JaimeOrtegaxyz/artisans-memphis/output/color/01_ARCH_DOME.png

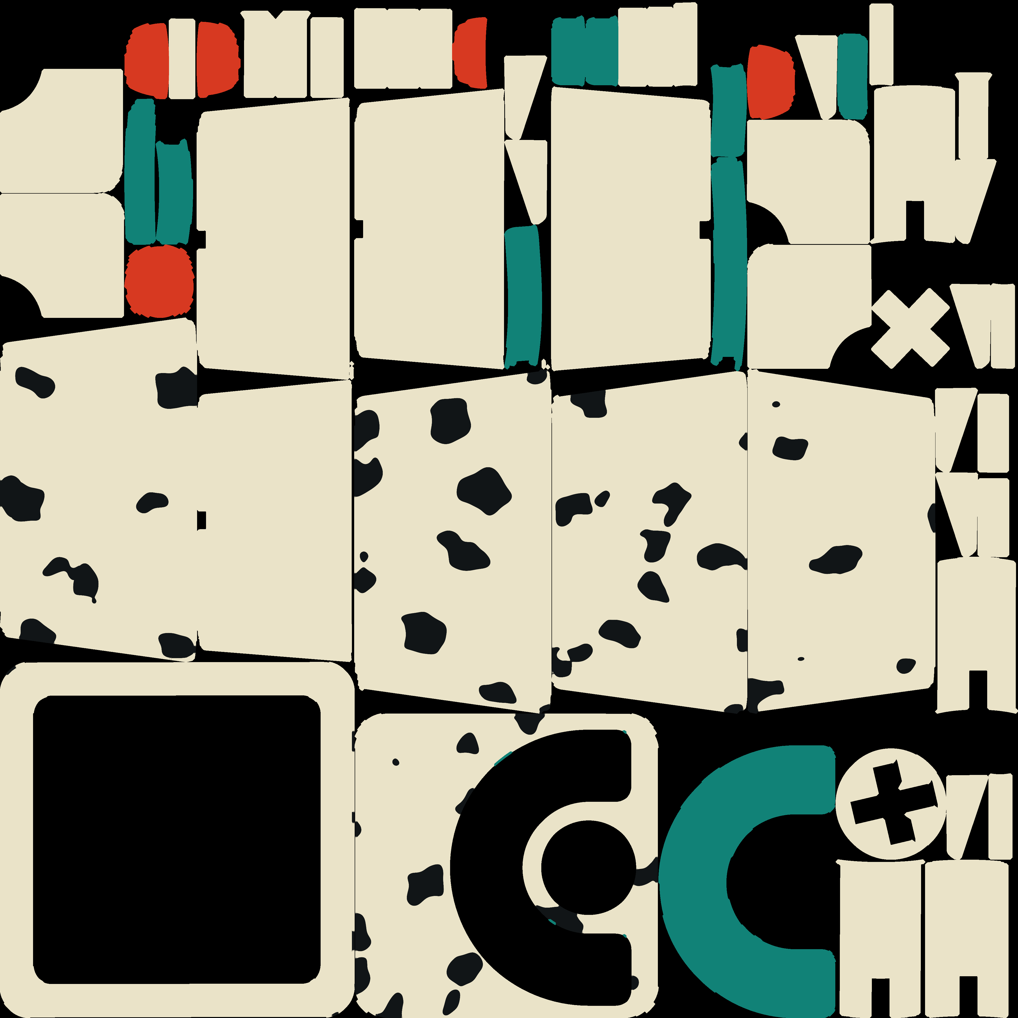
output/color/01_ARCH_DOME.png
