JaimeOrtegaxyz/artisans-memphis/output/color/02_ZIGZAG_CYLINDER.png

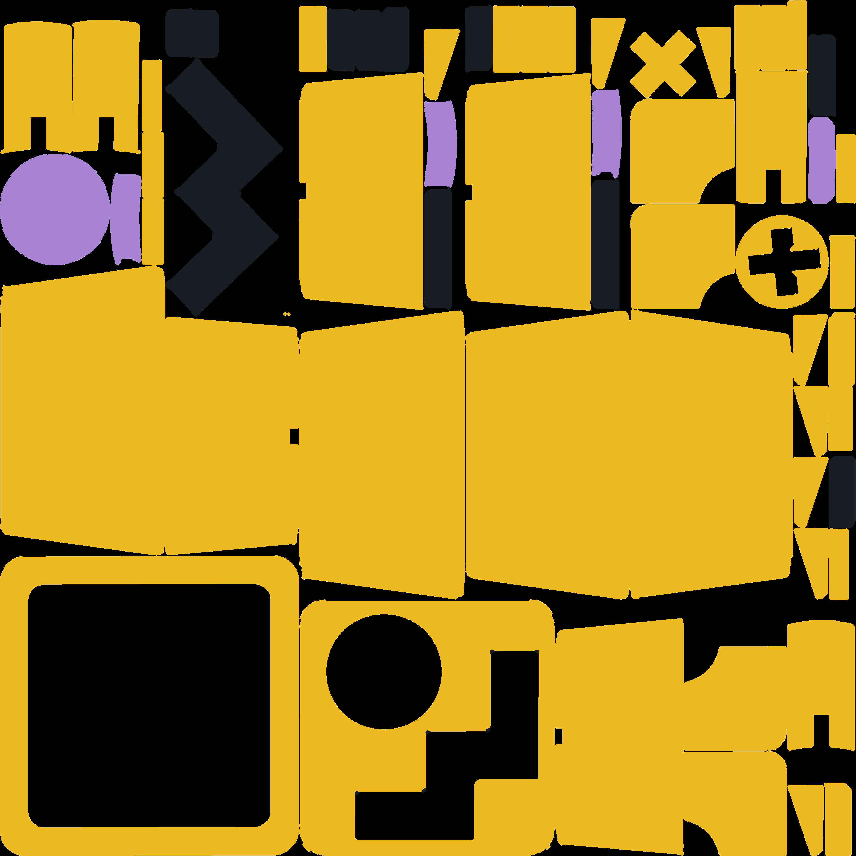
output/color/02_ZIGZAG_CYLINDER.png
