JaimeOrtegaxyz/artisans-memphis/output/color/03_DISC_RAILS.png

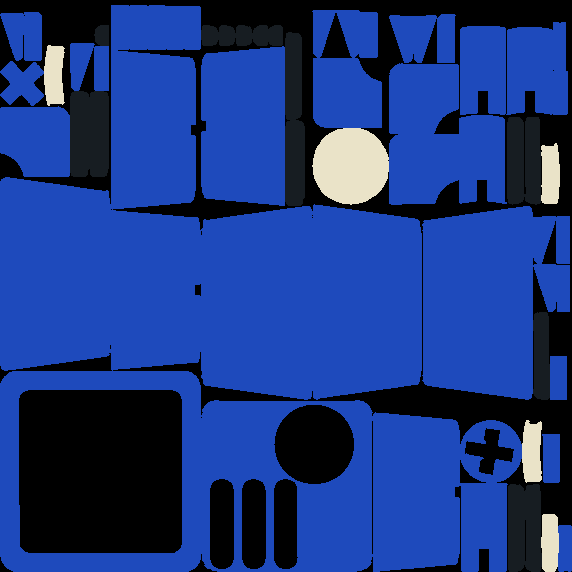
output/color/03_DISC_RAILS.png
