JaimeOrtegaxyz/artisans-memphis/output/color/04_STAIR_SILHOUETTE.png

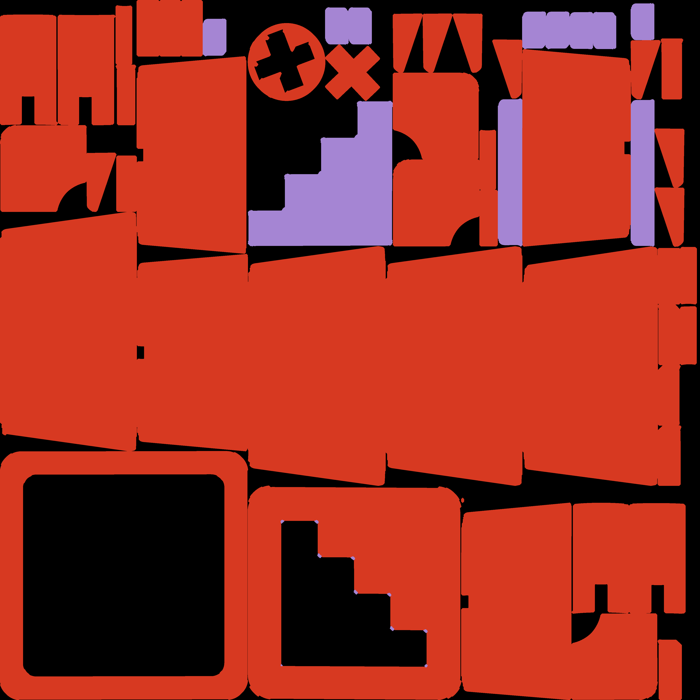
output/color/04_STAIR_SILHOUETTE.png
