JaimeOrtegaxyz/artisans-memphis/output/color/Color_Preview.png

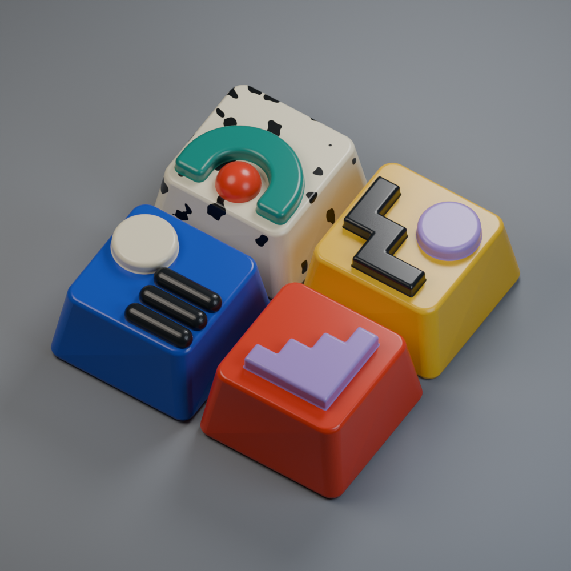
output/color/Color_Preview.png
