JaimeOrtegaxyz/artisans-memphis/output/drawings/04_STAIR_SILHOUETTE.png

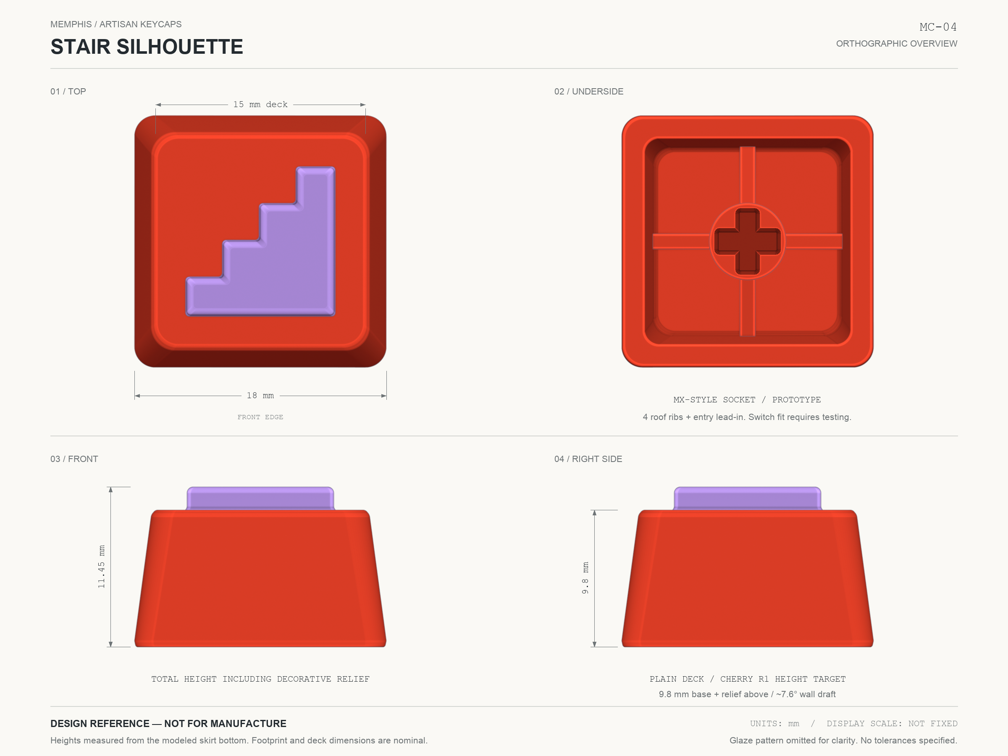
output/drawings/04_STAIR_SILHOUETTE.png
