JaimeOrtegaxyz/artisans-memphis/output/Memphis_Top.png

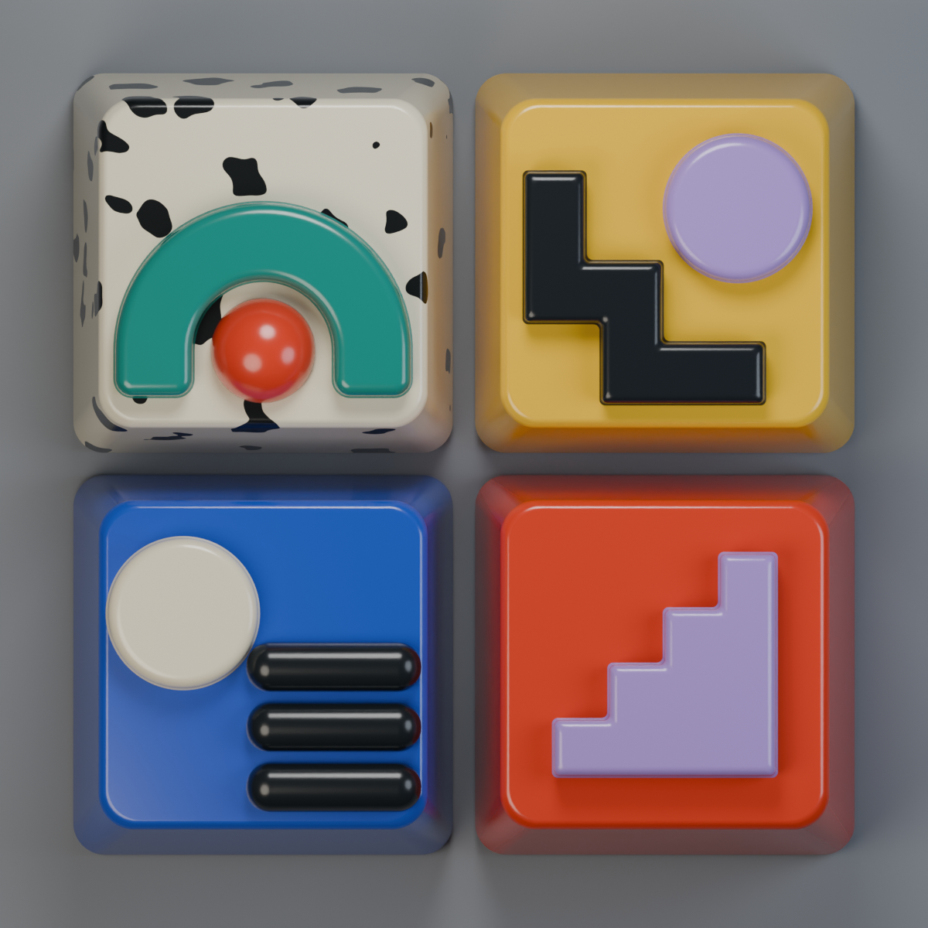
output/Memphis_Top.png
