JaimeOrtegaxyz/artisans-memphis/output/Memphis_Underside.png

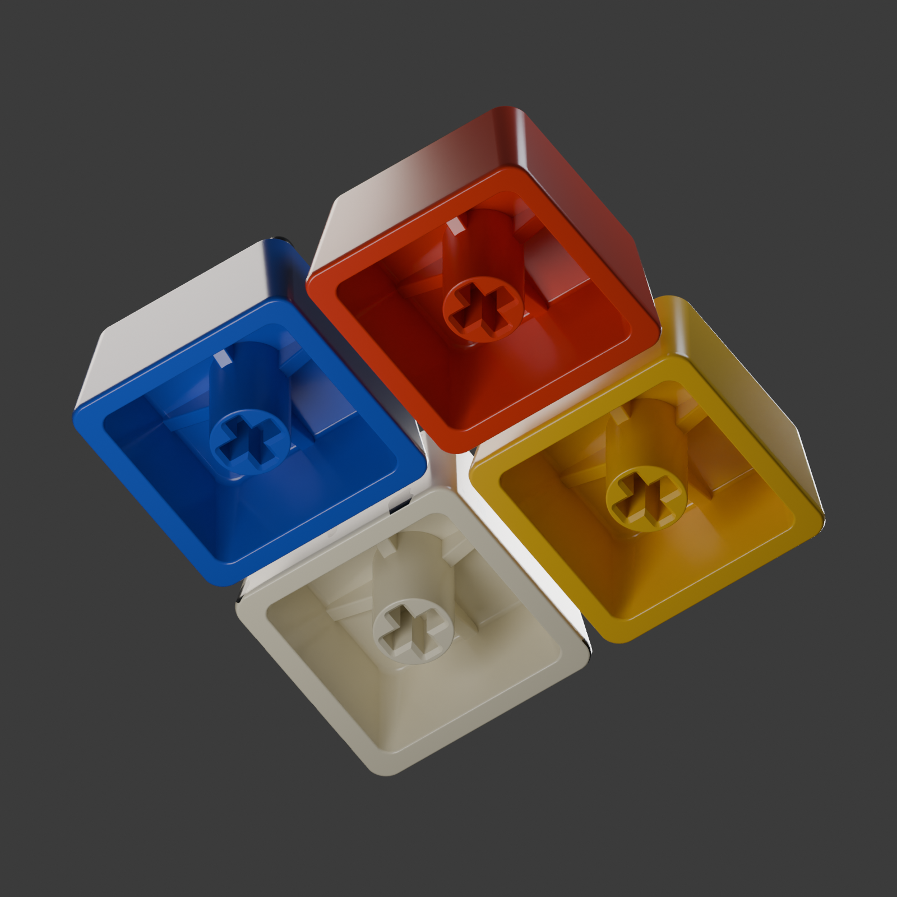
output/Memphis_Underside.png
