JaimeOrtegaxyz/artisans-memphis/output/color/00_BASE_FIT_TEST.png

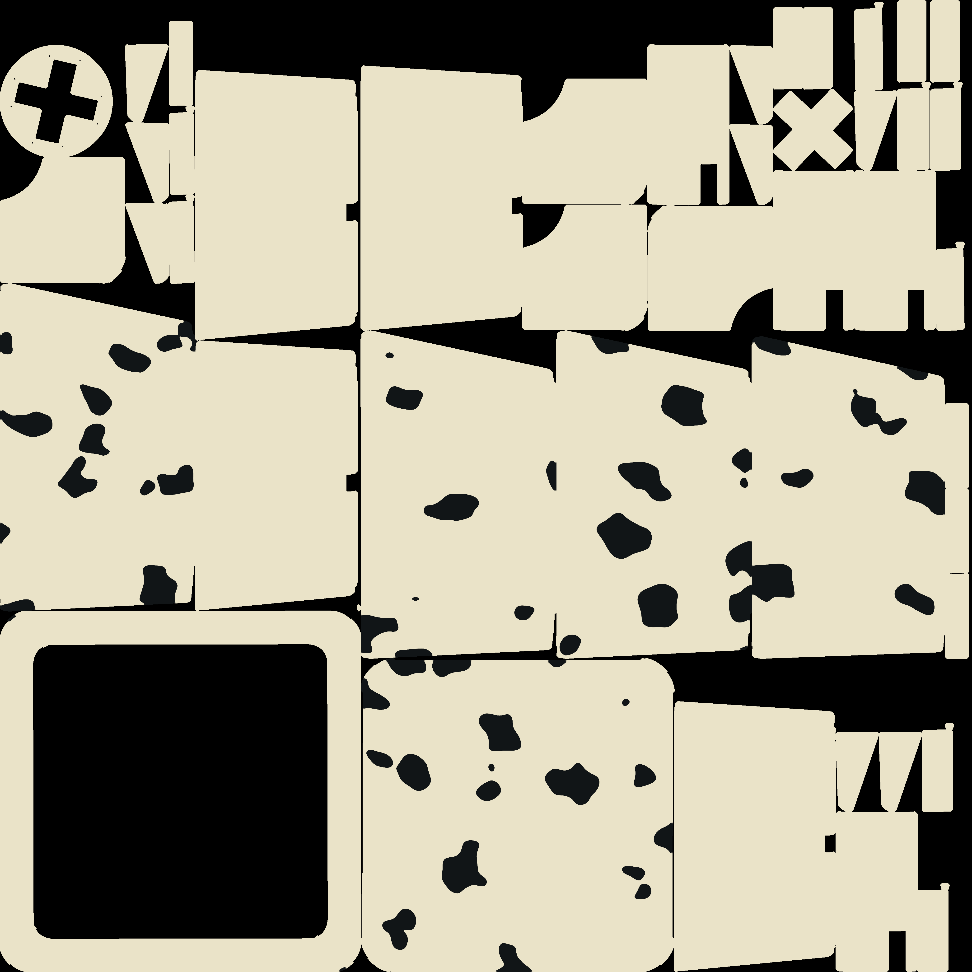
output/color/00_BASE_FIT_TEST.png
